Jay-Tai/Jay-Tab/Software/Raw images/New screens/Home screen.png

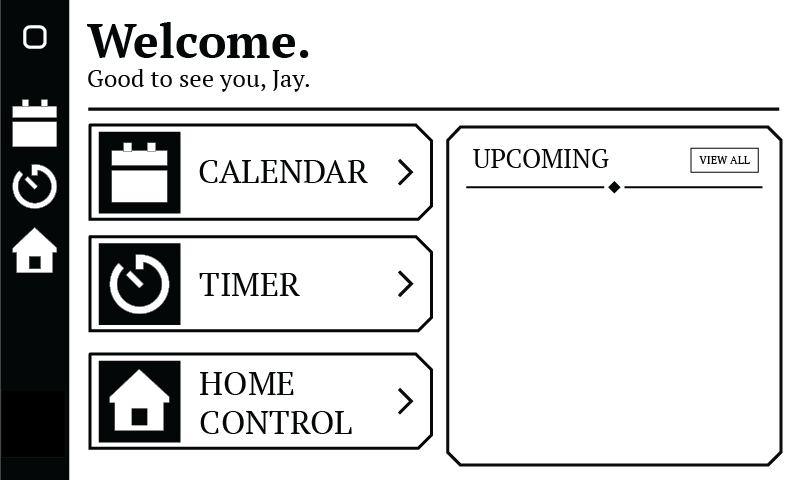
Software/Raw images/New screens/Home screen.png
